jzofalltrades/Q-dex/dataset/squirtle/32_shopping (1).png

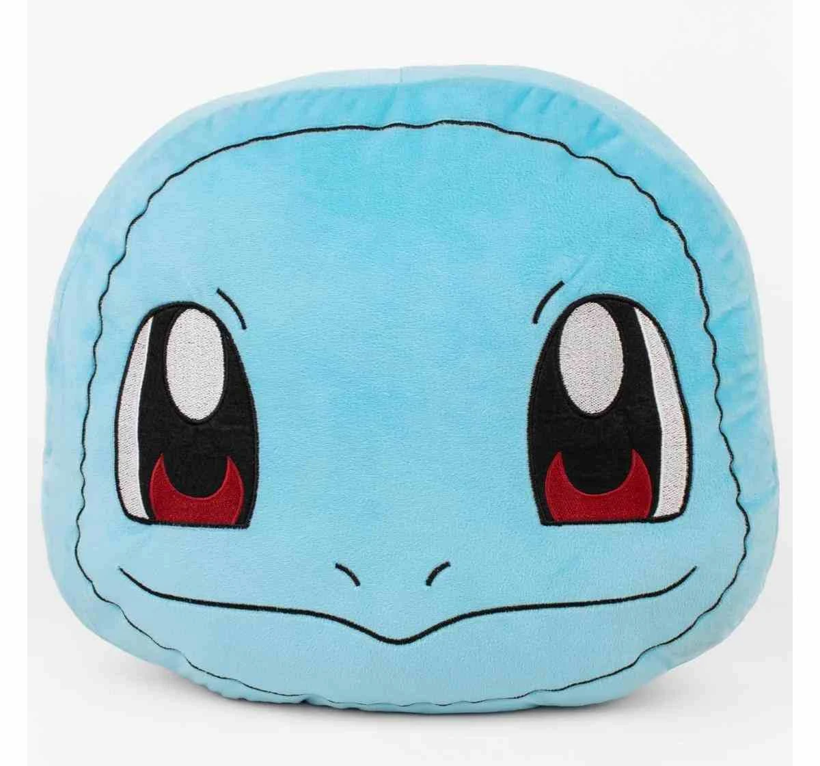
dataset/squirtle/32_shopping (1).png
