jzofalltrades/Q-dex/CAD/glb/glb_preview.png

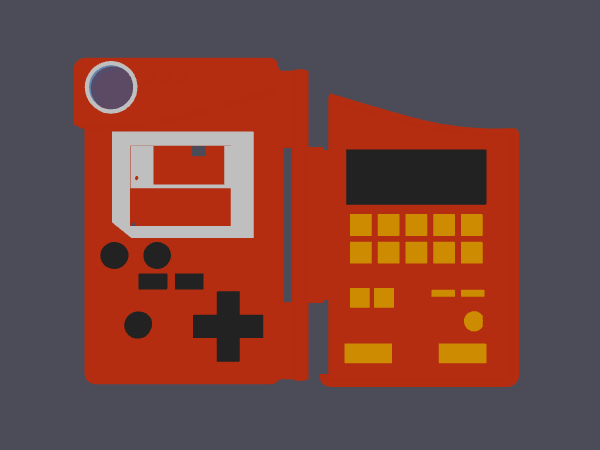
CAD/glb/glb_preview.png
