jzofalltrades/Q-dex/captures/capture_1787355873.jpg

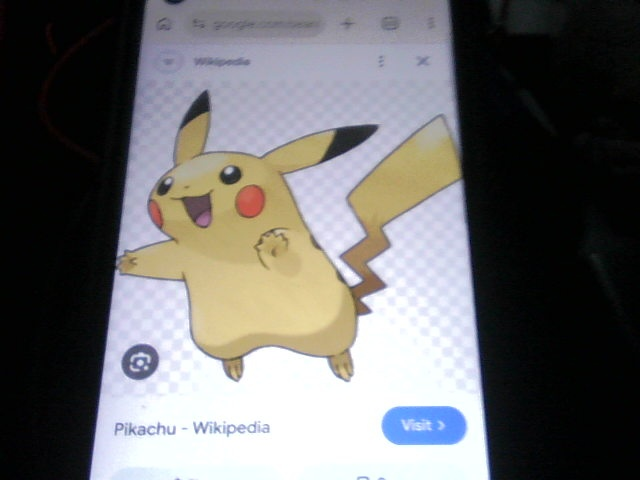
captures/capture_1787355873.jpg
