jzofalltrades/Q-dex/captures/capture_1787391064.jpg

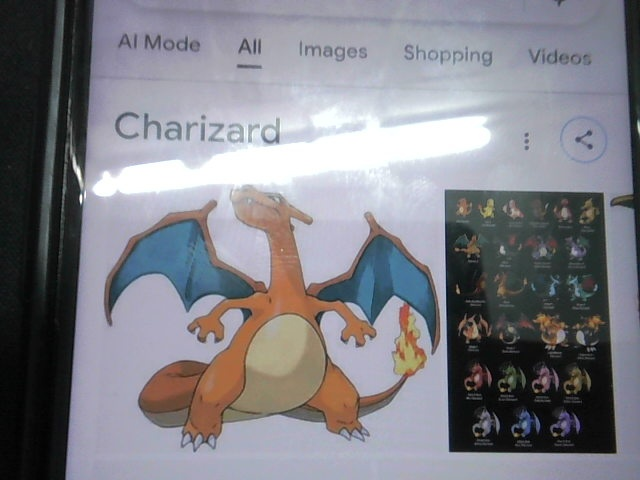
captures/capture_1787391064.jpg
