jzofalltrades/Q-dex/dataset/squirtle/1_1.png

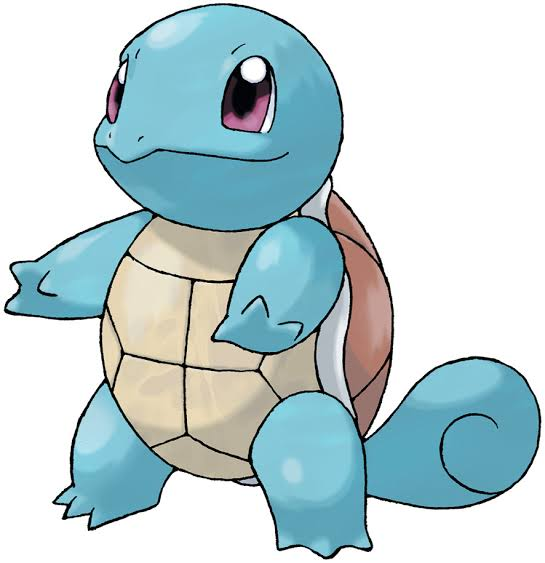
dataset/squirtle/1_1.png
