jzofalltrades/Q-dex/dataset/squirtle/2_1000076157-600x623.png

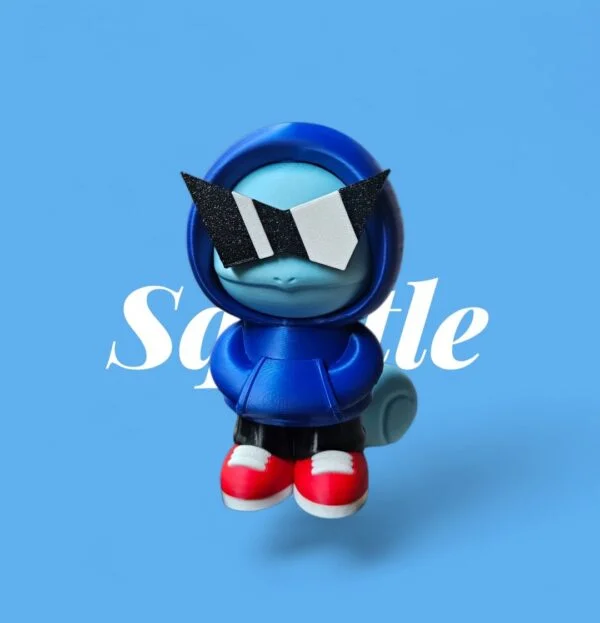
dataset/squirtle/2_1000076157-600x623.png
