jzofalltrades/Q-dex/dataset/squirtle/3_images (1).png

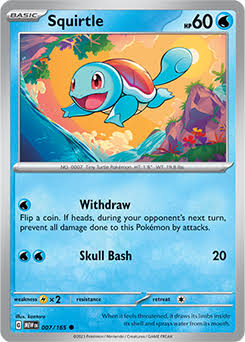
dataset/squirtle/3_images (1).png
