jzofalltrades/Q-dex/dataset/squirtle/4_images (10).png

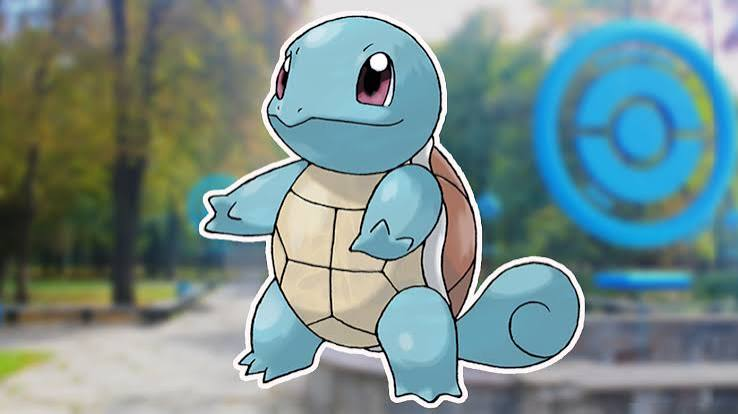
dataset/squirtle/4_images (10).png
