jzofalltrades/Q-dex/dataset/squirtle/5_images (11).png

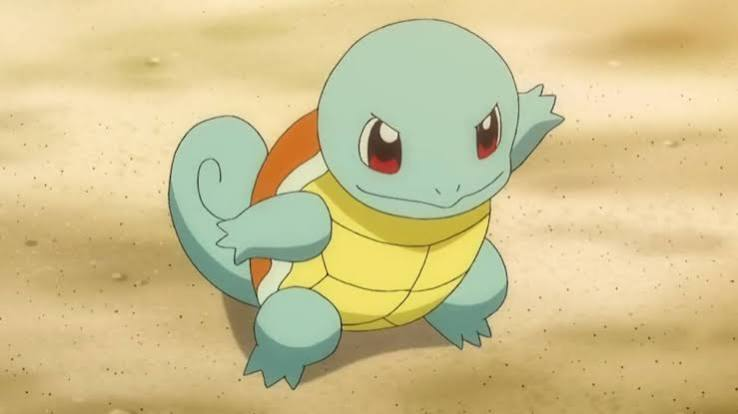
dataset/squirtle/5_images (11).png
