jzofalltrades/Q-dex/dataset/squirtle/6_images (12).png

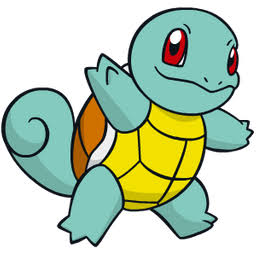
dataset/squirtle/6_images (12).png
