jzofalltrades/Q-dex/dataset/squirtle/8_images (14).png

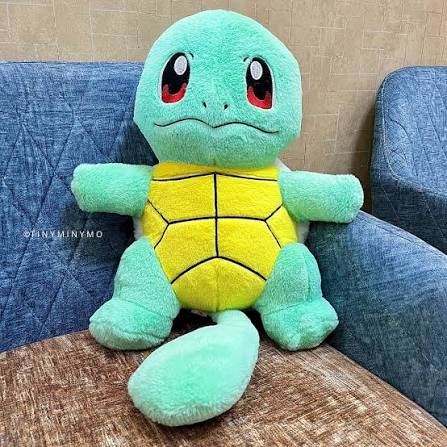
dataset/squirtle/8_images (14).png
