jzofalltrades/Q-dex/dataset/squirtle/9_images (15).png

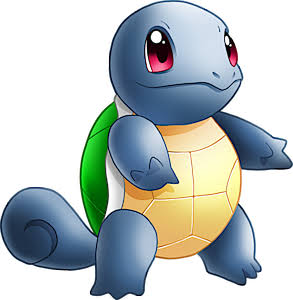
dataset/squirtle/9_images (15).png
