jzofalltrades/Q-dex/dataset/squirtle/10_images (16).png

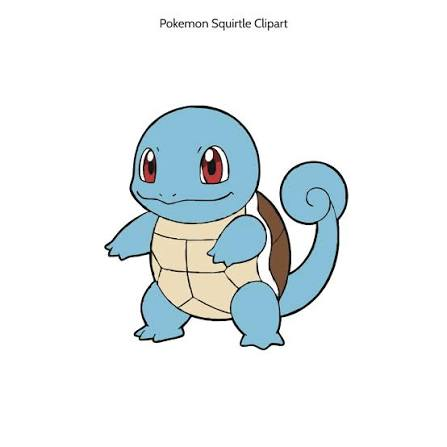
dataset/squirtle/10_images (16).png
