jzofalltrades/Q-dex/dataset/squirtle/11_images (17).png

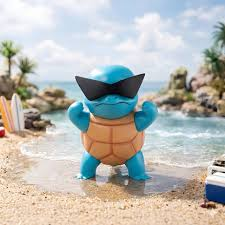
dataset/squirtle/11_images (17).png
