jzofalltrades/Q-dex/dataset/squirtle/12_images (18).png

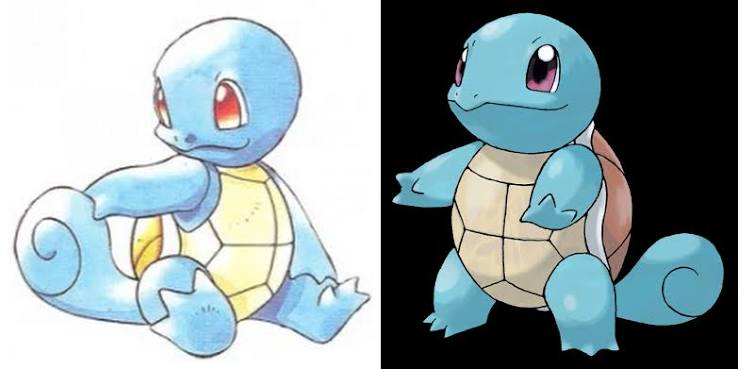
dataset/squirtle/12_images (18).png
