jzofalltrades/Q-dex/dataset/squirtle/13_images (19).png

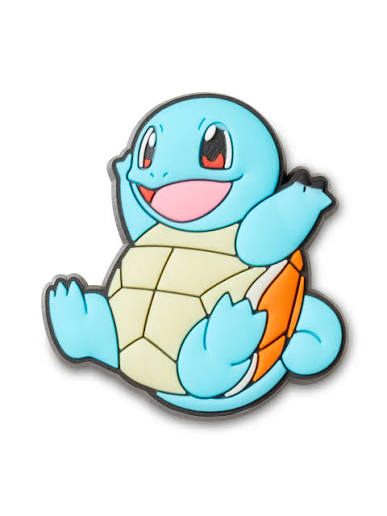
dataset/squirtle/13_images (19).png
