jzofalltrades/Q-dex/dataset/squirtle/14_images (2).png

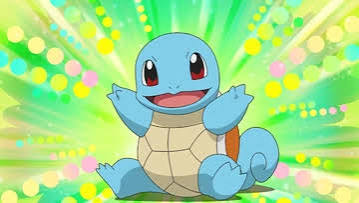
dataset/squirtle/14_images (2).png
