jzofalltrades/Q-dex/dataset/squirtle/15_images (20).png

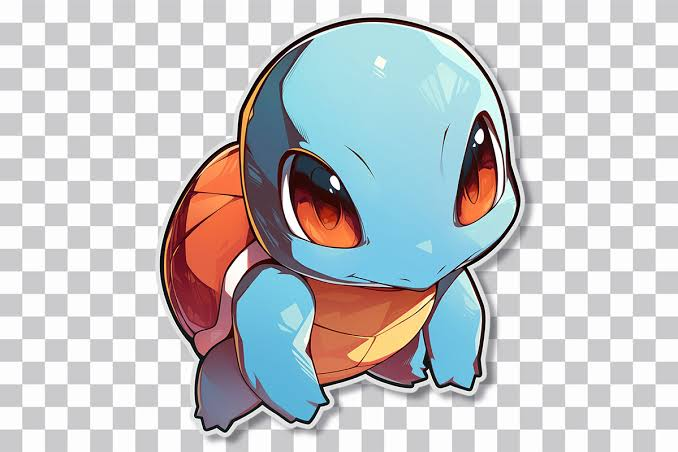
dataset/squirtle/15_images (20).png
