jzofalltrades/Q-dex/dataset/squirtle/16_images (21).png

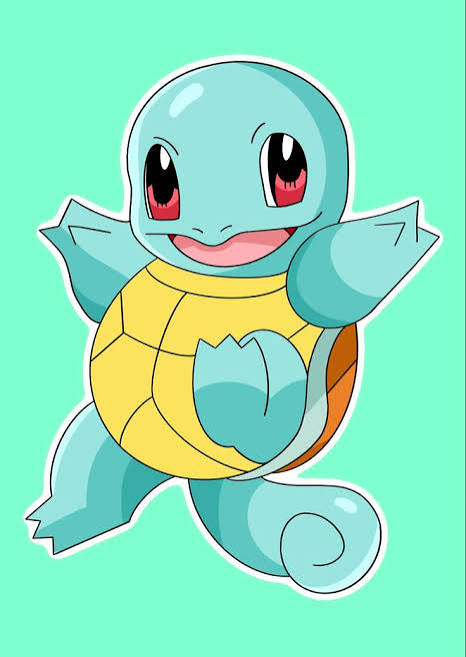
dataset/squirtle/16_images (21).png
