jzofalltrades/Q-dex/dataset/squirtle/17_images (22).png

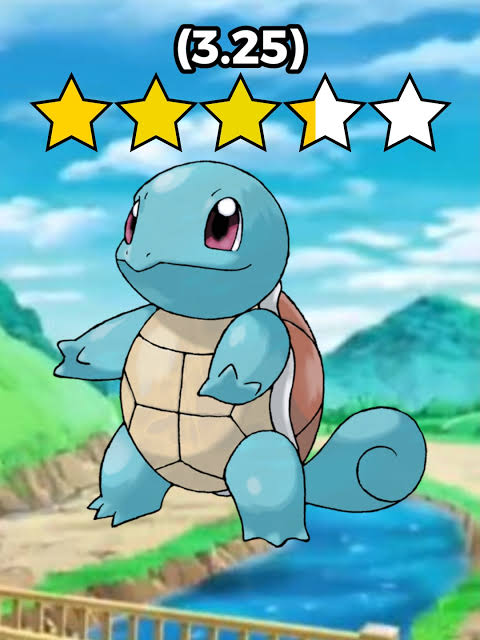
dataset/squirtle/17_images (22).png
