jzofalltrades/Q-dex/dataset/squirtle/18_images (23).png

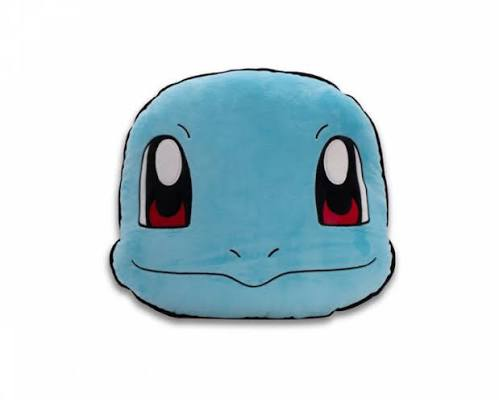
dataset/squirtle/18_images (23).png
