jzofalltrades/Q-dex/dataset/squirtle/19_images (24).png

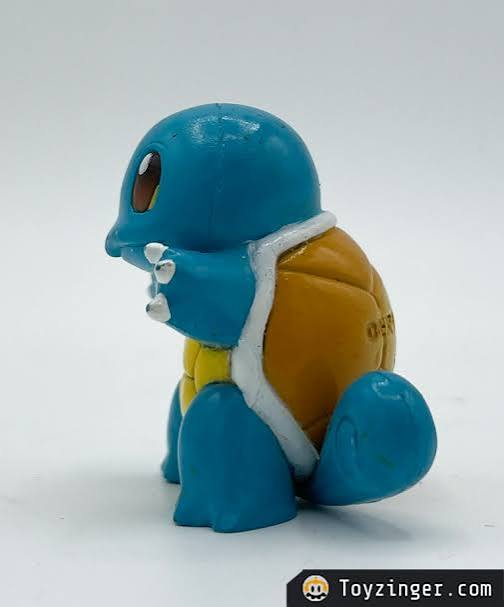
dataset/squirtle/19_images (24).png
