jzofalltrades/Q-dex/dataset/squirtle/20_images (25).png

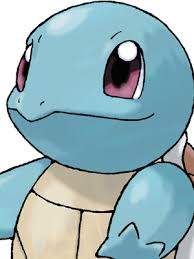
dataset/squirtle/20_images (25).png
