jzofalltrades/Q-dex/dataset/squirtle/21_images (26).png

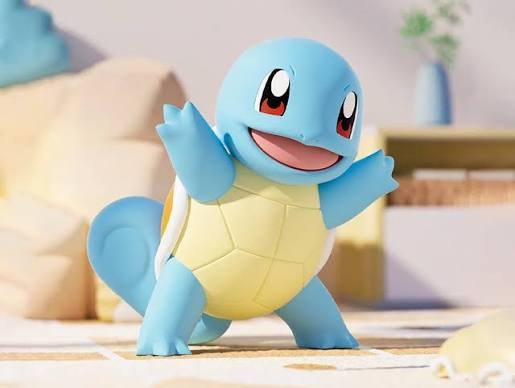
dataset/squirtle/21_images (26).png
