jzofalltrades/Q-dex/dataset/squirtle/22_images (27).png

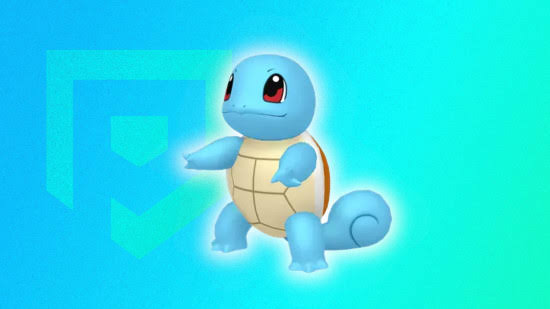
dataset/squirtle/22_images (27).png
