jzofalltrades/Q-dex/dataset/squirtle/23_images (28).png

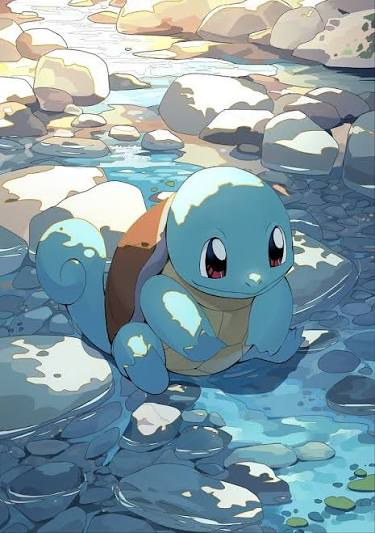
dataset/squirtle/23_images (28).png
