jzofalltrades/Q-dex/dataset/squirtle/24_images (3).png

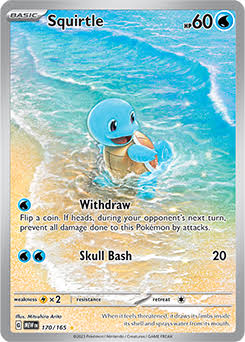
dataset/squirtle/24_images (3).png
