jzofalltrades/Q-dex/dataset/squirtle/25_images (4).png

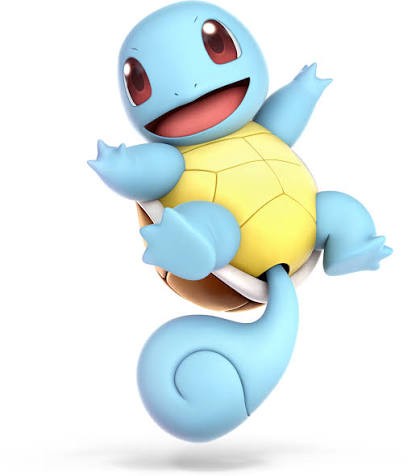
dataset/squirtle/25_images (4).png
