jzofalltrades/Q-dex/dataset/squirtle/26_images (5).png

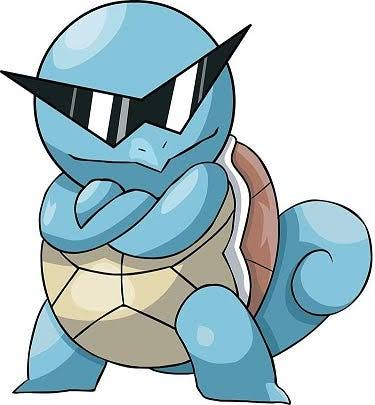
dataset/squirtle/26_images (5).png
