jzofalltrades/Q-dex/dataset/squirtle/27_images (6).png

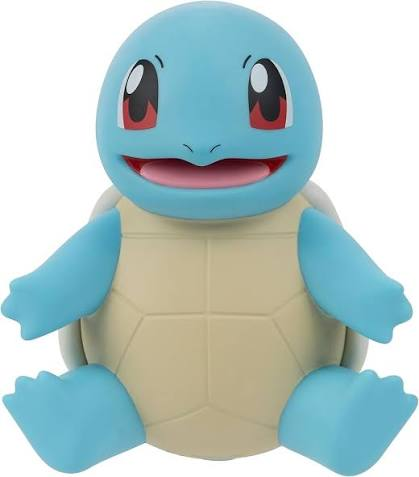
dataset/squirtle/27_images (6).png
