jzofalltrades/Q-dex/dataset/squirtle/30_images (9).png

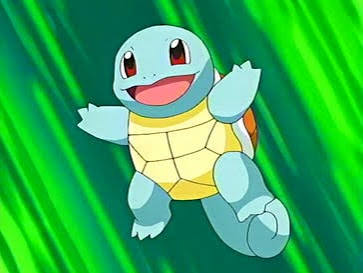
dataset/squirtle/30_images (9).png
