jzofalltrades/Q-dex/dataset/squirtle/31_images.png

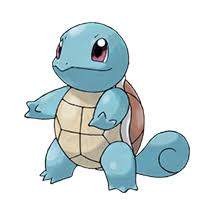
dataset/squirtle/31_images.png
