jzofalltrades/Q-dex/images/device-front-menu.jpg

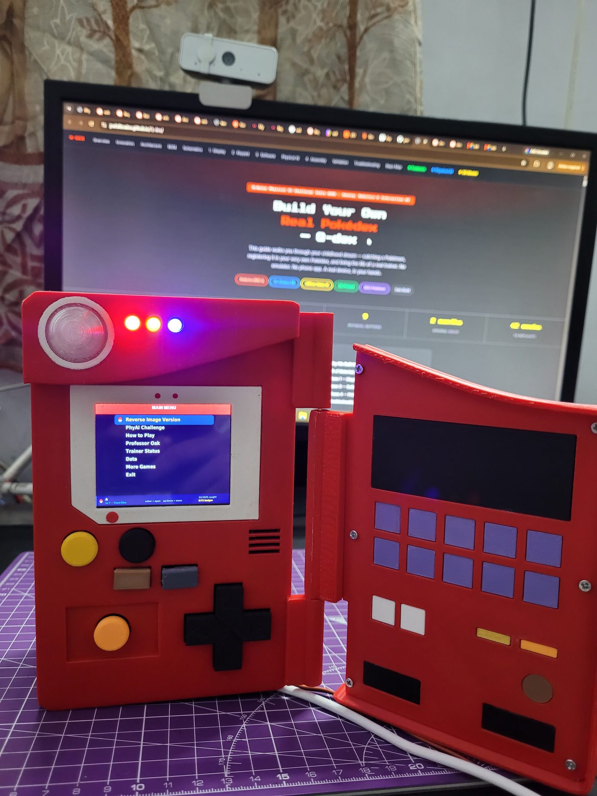
images/device-front-menu.jpg
