jzofalltrades/Q-dex/images/device-front-website.jpg

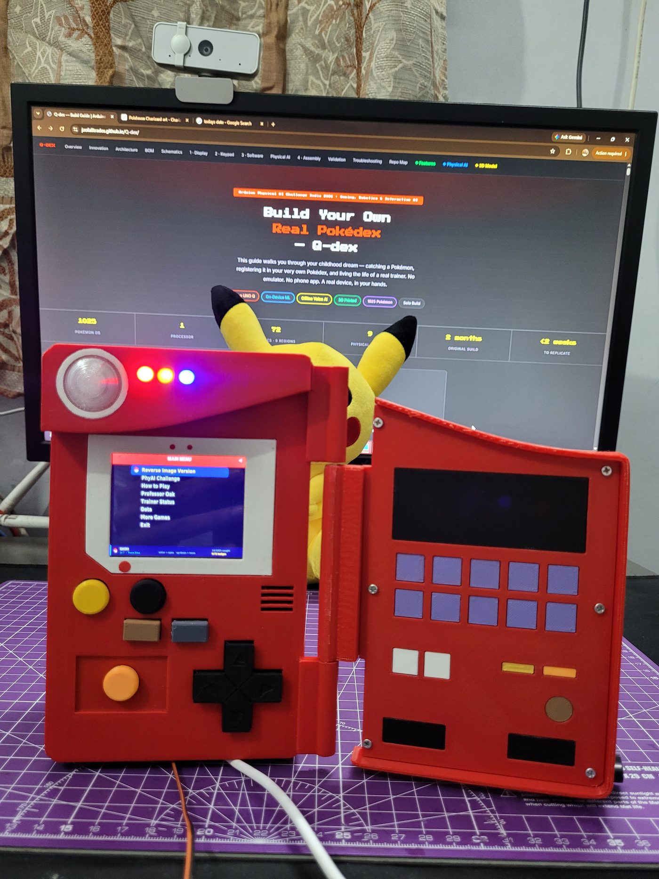
images/device-front-website.jpg
