jzofalltrades/Q-dex/images/device-open-menu.jpg

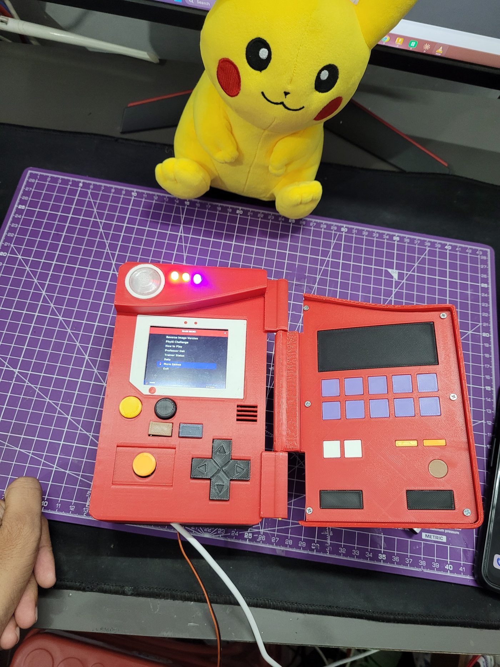
images/device-open-menu.jpg
