jzofalltrades/Q-dex/images/device-standing-leds.jpg

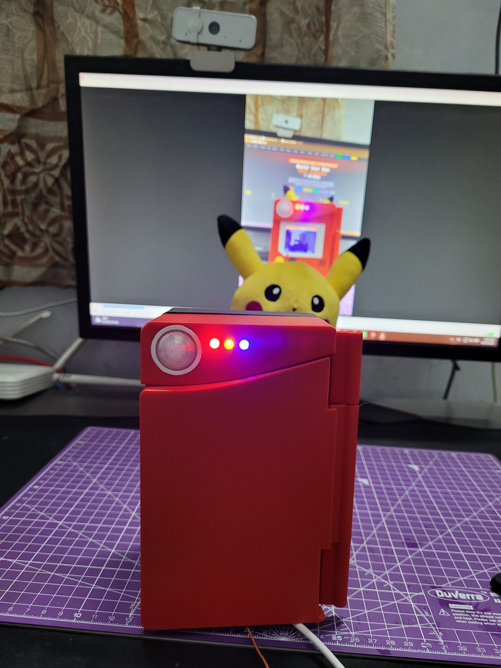
images/device-standing-leds.jpg
