jzofalltrades/Q-dex/images/entry-pikachu-stats.jpg

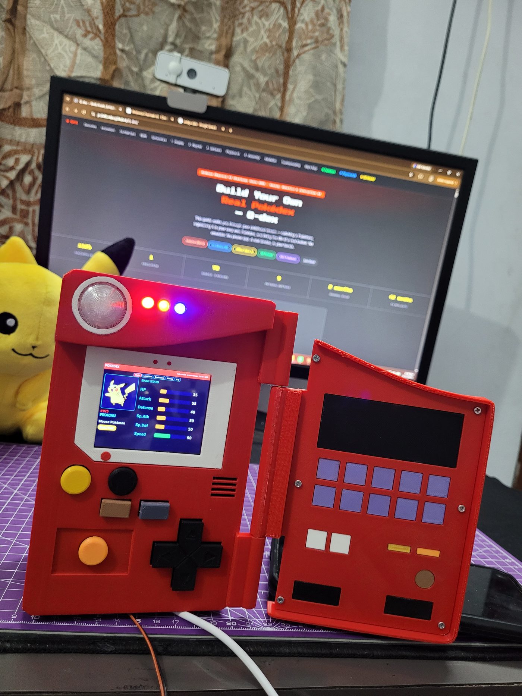
images/entry-pikachu-stats.jpg
