jzofalltrades/Q-dex/images/screens/game-flappy.png

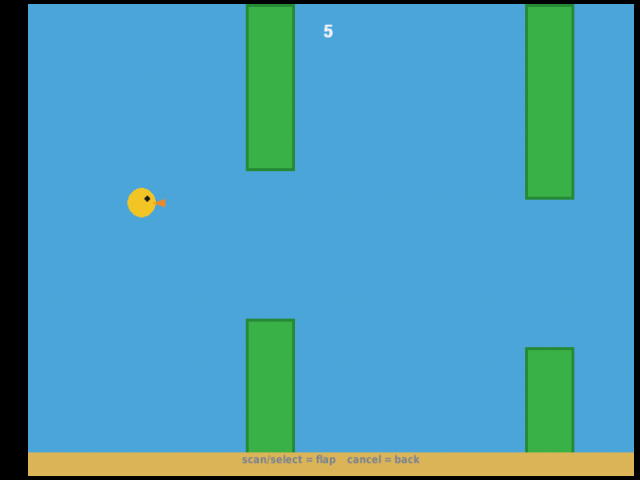
images/screens/game-flappy.png
