jzofalltrades/Q-dex/images/screens/menu-more-games.png

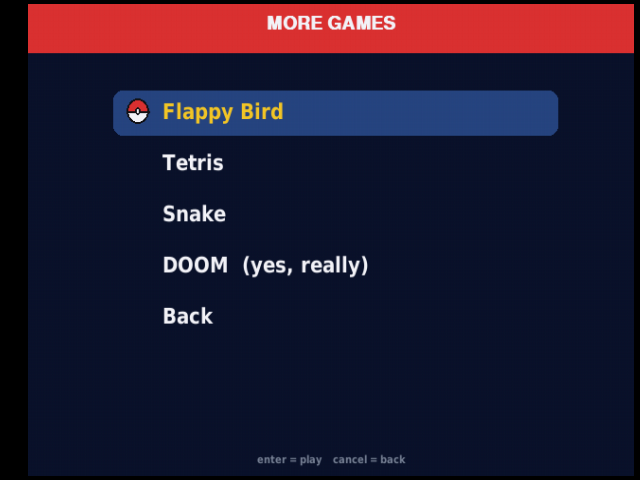
images/screens/menu-more-games.png
