jzofalltrades/Q-dex/dataset/squirtle/33_shopping (2).png

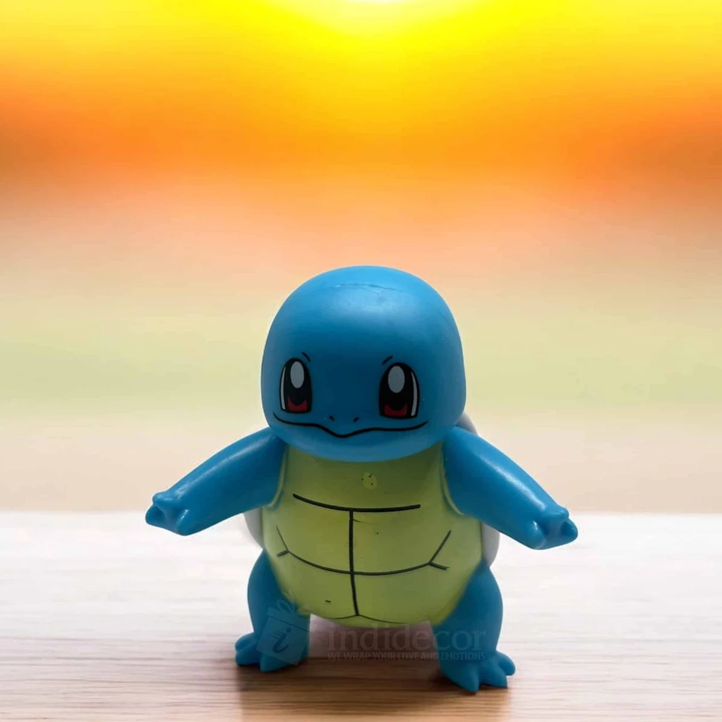
dataset/squirtle/33_shopping (2).png
