jzofalltrades/Q-dex/dataset/squirtle/34_shopping (3).png

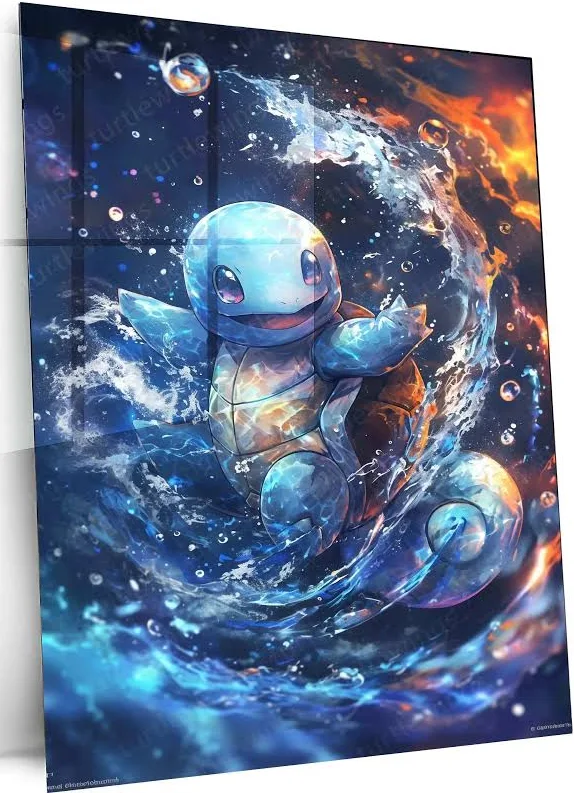
dataset/squirtle/34_shopping (3).png
