jzofalltrades/Q-dex/dataset/squirtle/35_shopping (4).png

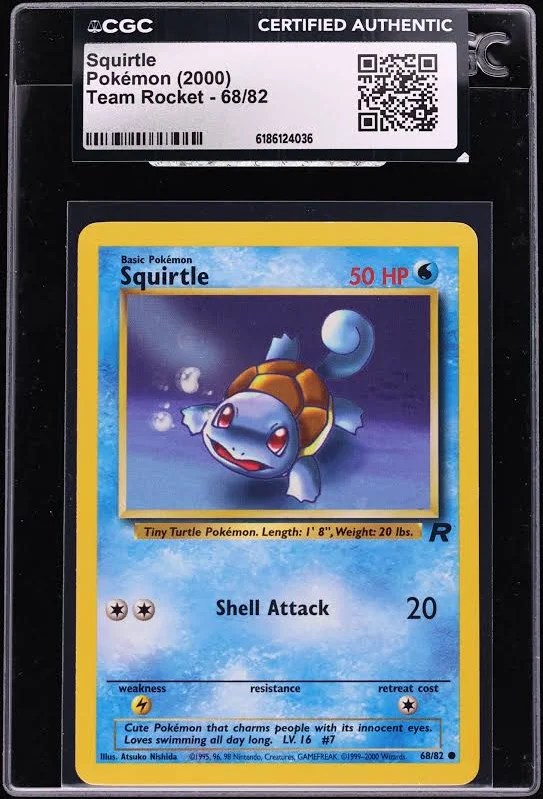
dataset/squirtle/35_shopping (4).png
