jzofalltrades/Q-dex/dataset/squirtle/36_shopping (5).png

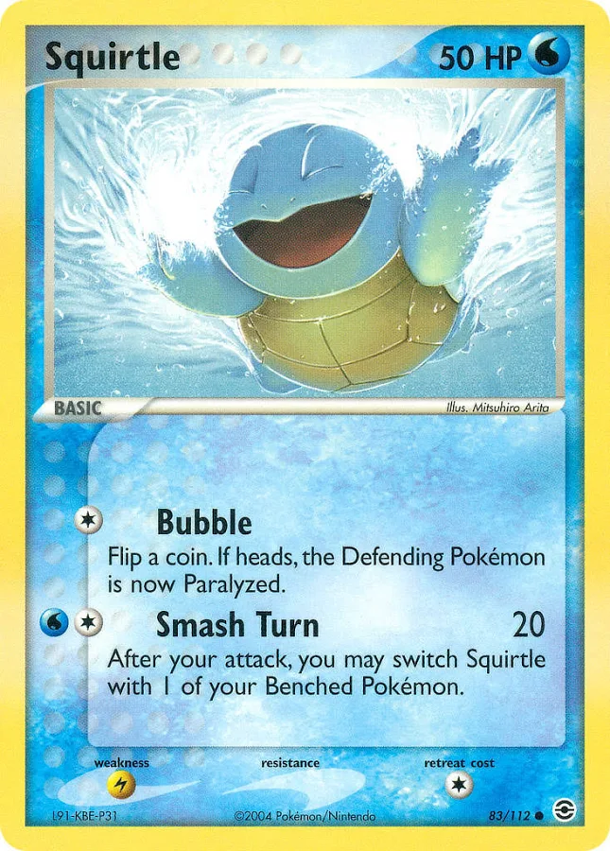
dataset/squirtle/36_shopping (5).png
