jzofalltrades/Q-dex/dataset/squirtle/37_shopping (6).png

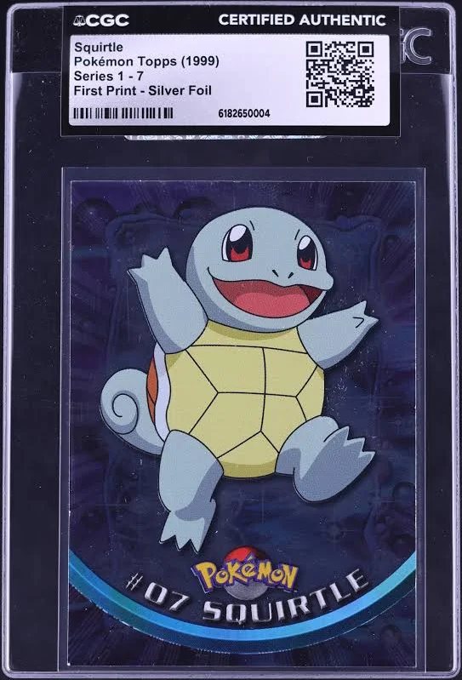
dataset/squirtle/37_shopping (6).png
