jzofalltrades/Q-dex/dataset/squirtle/38_shopping.png

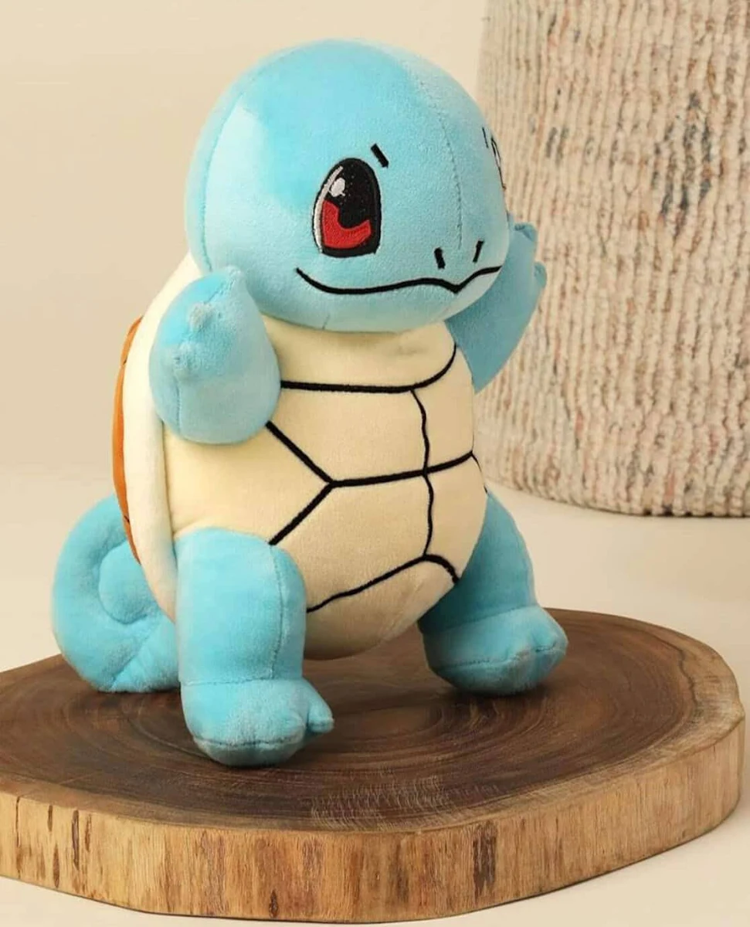
dataset/squirtle/38_shopping.png
