jzofalltrades/Q-dex/CAD/3mf/Dome_Ring.3mf

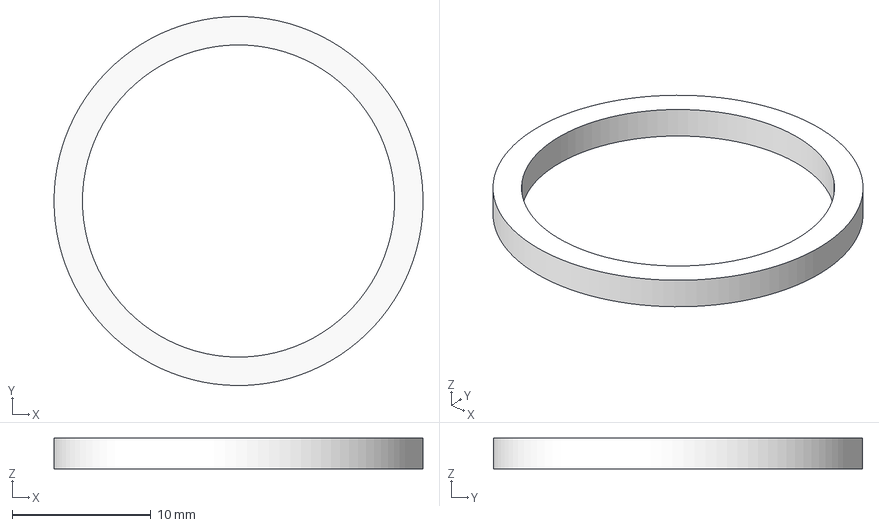
[picture p64: CAD file, 2026-09-16]
CAD/3mf/Dome_Ring.3mf
26.6 x 26.6 x 2.20 mm
