jzofalltrades/Q-dex/CAD/3mf/Cap_Select.3mf

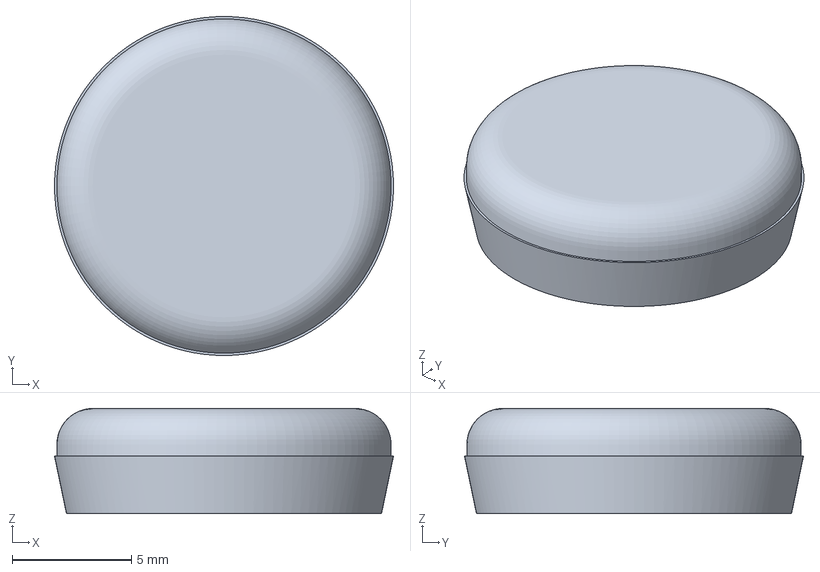
[picture p65: CAD file, 2026-09-16]
CAD/3mf/Cap_Select.3mf
14.2 x 14.2 x 4.40 mm
