jzofalltrades/Q-dex/CAD/3mf/Cap_pillB.3mf

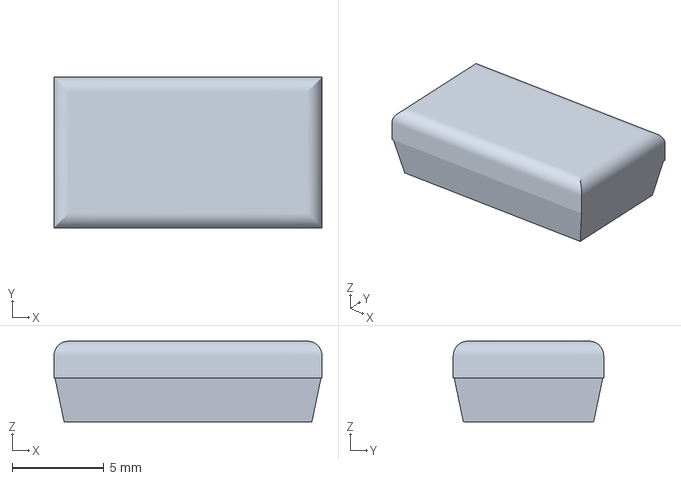
[picture p66: CAD file, 2026-09-16]
CAD/3mf/Cap_pillB.3mf
14.6 x 8.20 x 4.40 mm
