jzofalltrades/Q-dex/CAD/3mf/LidFacePlate.3mf

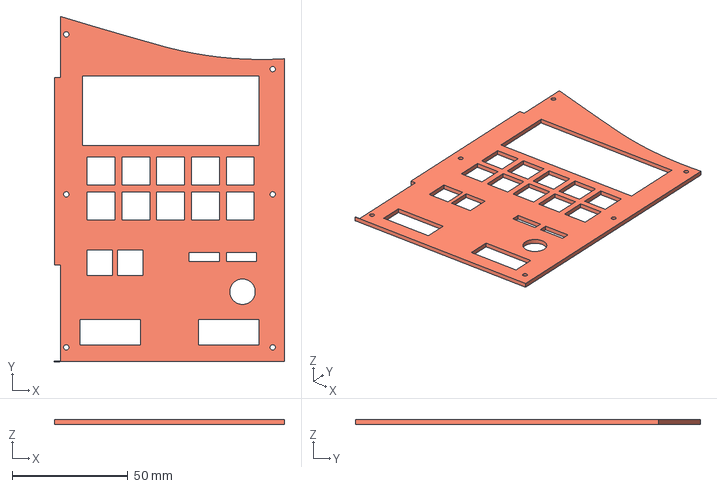
[picture p67: CAD file, 2026-09-16]
CAD/3mf/LidFacePlate.3mf
99.2 x 148.8 x 2.00 mm
