jzofalltrades/Q-dex/CAD/3mf/DummyBtn_Mute.3mf

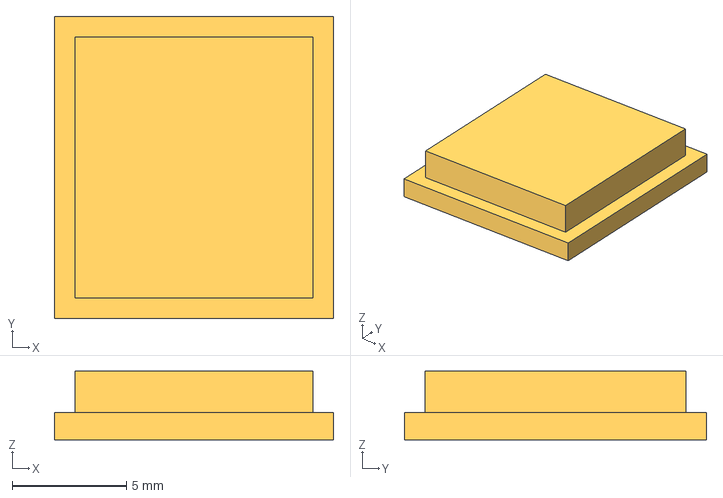
[picture p68: CAD file, 2026-09-16]
CAD/3mf/DummyBtn_Mute.3mf
12.2 x 13.2 x 3.00 mm
