jzofalltrades/Q-dex/CAD/3mf/ScreenBezel.3mf

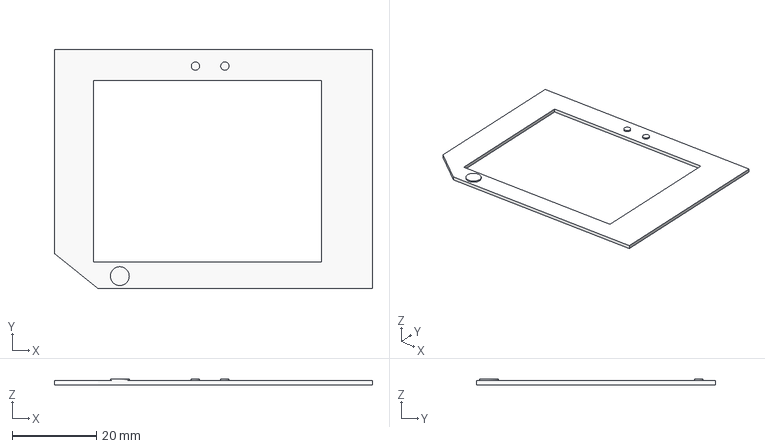
[picture p69: CAD file, 2026-09-16]
CAD/3mf/ScreenBezel.3mf
75.7 x 56.9 x 1.40 mm
