jzofalltrades/Q-dex/CAD/3mf/Cap_DPad.3mf

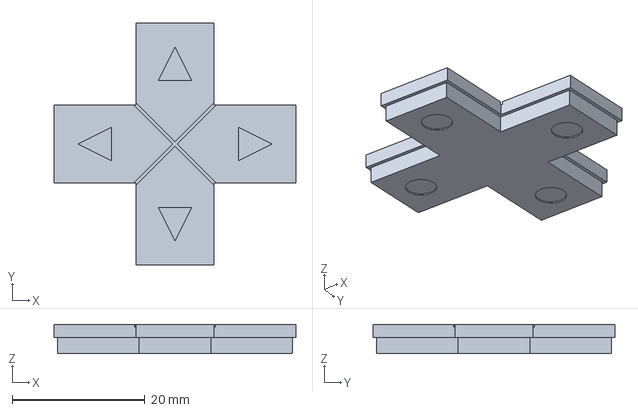
[picture p70: CAD file, 2026-09-16]
CAD/3mf/Cap_DPad.3mf
36.4 x 36.4 x 4.40 mm
