jzofalltrades/Q-dex/CAD/3mf/RightLid.3mf

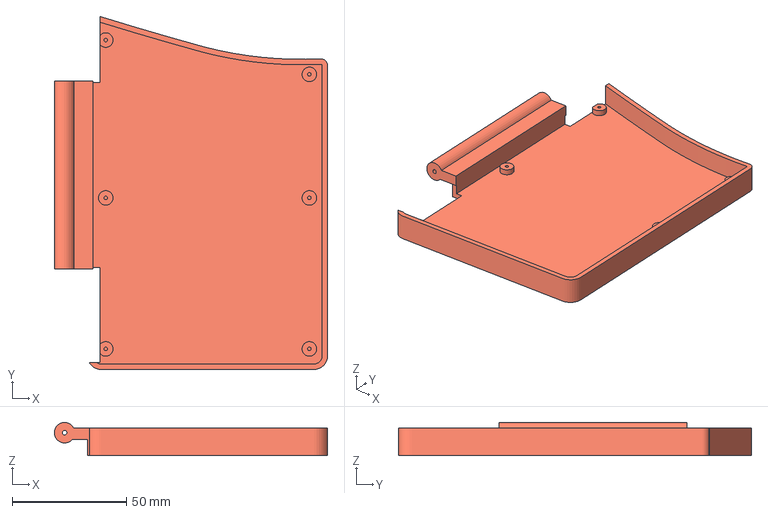
[picture p71: CAD file, 2026-09-16]
CAD/3mf/RightLid.3mf
119.5 x 154.3 x 14.5 mm
