jzofalltrades/Q-dex/CAD/3mf/LCDCrossPlate.3mf

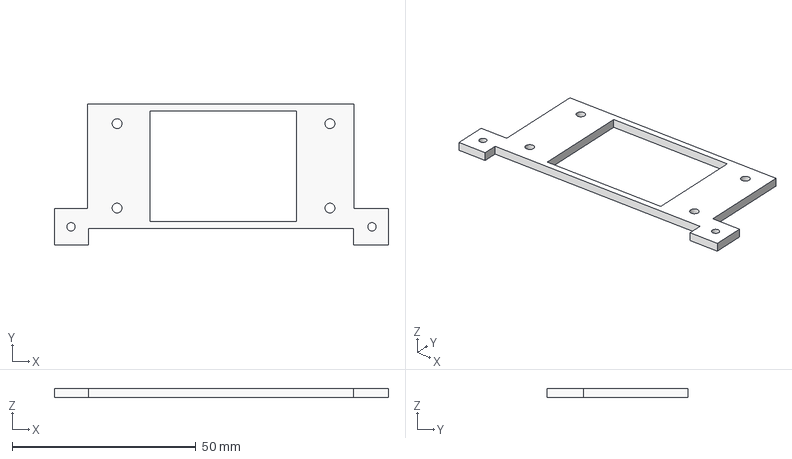
[picture p72: CAD file, 2026-09-16]
CAD/3mf/LCDCrossPlate.3mf
91.0 x 38.5 x 2.50 mm
